disobeyfi/badge-2019/hardware/kicad/rev2badge.sch

## KiCad design hardware/kicad/rev2badge.sch (2019-03-05)

Schematic: rev2badge.sch

Parts:
BT1: Battery; AAAx2holder
C1, C2, C3, C4, C5, C6, C7, C8, C9: 10u; C_0603
D1, D3, D4, D5, D6, D7: LED_ARGB; ARGB-0606
D2: LED_Small_ALT; LED_1206_HandSoldering
J1: USB_OTG; MICROUSB
J2: Conn_01x30; ER-CON30HB-1
J3, J4, J5, J6, J7, J8: TEST_1P; Measurement_Point_Round-SMD-Pad_Big
J9: Conn_02x02_Counter_Clockwise; Pin_Header_Straight_2x02_Pitch2.54mm
J10: Conn_01x06; Pin_Header_Straight_1x06_Pitch2.54mm
J11: Conn_01x05; Pin_Header_Straight_1x05_Pitch2.54mm
L1: L; C_0805
LS1: Speaker_Crystal; Piezo-PS1240P02BT
R1, R2, R3, R14: 330R; R_0603
R4, R16: 2k; R_0603
R5: 1k; R_0603
R6, R7, R11, R12, R13, R15: 100k; R_0603
R8, R9, R10: 4.7k; R_0603
SW1, SW2: SW_Push; SW_SPST_FSMSM
U1: ESP32-WROOM
U2: SAMD21G15A-MU; QFN-48-1EP_7x7mm_Pitch0.5mm
U3: AZ1117-3.3; SOT-223-3_TabPin2
U4: TSMP58000; IRReceiver_Vishay_MINICAST-3pin
U5: AAT1217ICA-3.3-T1; TSOT-23-6
U6: MCP6001; SOT-23-5
