disobeyfi/badge-2019/src/samd/1.6.18/variants/disobey/variant.cpp

/*
  Copyright (c) 2014-2015 Arduino LLC.  All right reserved.

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
  You should have received a copy of the GNU Lesser General Public
  License along with this library; if not, write to the Free Software
  Foundation, Inc., 51 Franklin St, Fifth Floor, Boston, MA  02110-1301  USA
*/


#include "variant.h"

/*
 * Pins descriptions
 */
const PinDescription g_APinDescription[]=
{
  // 0..13 - Digital pins
  // ----------------------
  // 0/1 - SERCOM/UART (Serial1)
  { PORTA,  1, PIO_SERCOM_ALT, 0, No_ADC_Channel, NOT_ON_PWM, NOT_ON_TIMER, EXTERNAL_INT_NONE }, // PA01 / UART RX
  { PORTA,  0, PIO_SERCOM_ALT, 0, No_ADC_Channel, NOT_ON_PWM, NOT_ON_TIMER, EXTERNAL_INT_NONE }, // PA00 / UART TX

  // 2..24
  // Digital Low
  { PORTA,  18, PIO_TIMER_ALT, (PIN_ATTR_DIGITAL|PIN_ATTR_PWM|PIN_ATTR_TIMER_ALT), No_ADC_Channel, PWM0_CH2, TCC0_CH2, EXTERNAL_INT_NONE }, // D2 LED
  { PORTA,  23, PIO_TIMER_ALT, (PIN_ATTR_DIGITAL|PIN_ATTR_PWM|PIN_ATTR_TIMER_ALT), No_ADC_Channel, PWM0_CH5, TCC0_CH5, EXTERNAL_INT_NONE }, // D3 LED
  { PORTA,  22, PIO_TIMER_ALT, (PIN_ATTR_DIGITAL|PIN_ATTR_PWM|PIN_ATTR_TIMER_ALT), No_ADC_Channel, PWM0_CH4, TCC0_CH4, EXTERNAL_INT_NONE }, // D4 LED
  { PORTA,  21, PIO_TIMER_ALT, (PIN_ATTR_DIGITAL|PIN_ATTR_PWM|PIN_ATTR_TIMER_ALT), No_ADC_Channel, PWM0_CH7, TCC0_CH7, EXTERNAL_INT_NONE }, // D5 LED
  { PORTA,  20, PIO_DIGITAL, (PIN_ATTR_DIGITAL), No_ADC_Channel, NOT_ON_PWM, NOT_ON_TIMER, EXTERNAL_INT_NONE }, // D6 LED
  { PORTA,  19, PIO_TIMER_ALT, (PIN_ATTR_DIGITAL|PIN_ATTR_PWM|PIN_ATTR_TIMER_ALT), No_ADC_Channel, PWM0_CH3, TCC0_CH3, EXTERNAL_INT_NONE }, // D7 LED
  { PORTA,  17, PIO_TIMER, (PIN_ATTR_DIGITAL|PIN_ATTR_PWM|PIN_ATTR_TIMER), No_ADC_Channel, PWM2_CH1, TCC2_CH1, EXTERNAL_INT_NONE }, // D8 LED R
  { PORTA,  12, PIO_TIMER, (PIN_ATTR_DIGITAL|PIN_ATTR_PWM|PIN_ATTR_TIMER), No_ADC_Channel, PWM2_CH0, TCC2_CH0, EXTERNAL_INT_NONE }, // D9 LED G
  { PORTA,  16, PIO_TIMER_ALT, (PIN_ATTR_DIGITAL|PIN_ATTR_PWM|PIN_ATTR_TIMER_ALT), No_ADC_Channel, PWM0_CH6, TCC0_CH6, EXTERNAL_INT_NONE }, // D10 LED B
  { PORTA, 28, PIO_DIGITAL, (PIN_ATTR_DIGITAL), No_ADC_Channel, NOT_ON_PWM, NOT_ON_TIMER, EXTERNAL_INT_8 },                    // D11 ESPBL
  { PORTA, 27, PIO_DIGITAL, (PIN_ATTR_DIGITAL), No_ADC_Channel, NOT_ON_PWM, NOT_ON_TIMER, EXTERNAL_INT_15 },                    // D12 ESPRST
  { PORTA, 13, PIO_DIGITAL, (PIN_ATTR_DIGITAL), No_ADC_Channel, NOT_ON_PWM, NOT_ON_TIMER, EXTERNAL_INT_13 },                    // D13 IRLED
  { PORTB,  10, PIO_TIMER, (PIN_ATTR_DIGITAL|PIN_ATTR_PWM|PIN_ATTR_TIMER), No_ADC_Channel, PWM5_CH0, TC5_CH0, EXTERNAL_INT_NONE }, // D14 SPEAKER_OUT
  { PORTA, 10, PIO_DIGITAL, (PIN_ATTR_DIGITAL), No_ADC_Channel, NOT_ON_PWM, NOT_ON_TIMER, EXTERNAL_INT_10 },                    // D15 LCDRST
  { PORTA,  11, PIO_TIMER, (PIN_ATTR_DIGITAL|PIN_ATTR_PWM|PIN_ATTR_TIMER), No_ADC_Channel, PWM1_CH1, TCC1_CH1, EXTERNAL_INT_NONE }, // D16 LCDBL
  { PORTA,  14, PIO_DIGITAL, (PIN_ATTR_DIGITAL), No_ADC_Channel, NOT_ON_PWM, NOT_ON_TIMER, EXTERNAL_INT_13 }, // D17
  { PORTA,  8, PIO_SERCOM, PIN_ATTR_DIGITAL, No_ADC_Channel, NOT_ON_PWM, NOT_ON_TIMER, EXTERNAL_INT_NMI },                    // D18/SDA
  { PORTA,  9, PIO_SERCOM, PIN_ATTR_DIGITAL, No_ADC_Channel, NOT_ON_PWM, NOT_ON_TIMER, EXTERNAL_INT_9 },                    // D19/SCL
  { PORTB, 22, PIO_DIGITAL, (PIN_ATTR_DIGITAL), No_ADC_Channel, NOT_ON_PWM, NOT_ON_TIMER, EXTERNAL_INT_6 },                    // D20
  { PORTB, 23, PIO_DIGITAL, (PIN_ATTR_DIGITAL), No_ADC_Channel, NOT_ON_PWM, NOT_ON_TIMER, EXTERNAL_INT_7 },                    // D21  
  { PORTA, 10, PIO_DIGITAL, (PIN_ATTR_DIGITAL), No_ADC_Channel, NOT_ON_PWM, NOT_ON_TIMER, EXTERNAL_INT_10 },                    // D22 DO NOT USE
  { PORTA, 15, PIO_DIGITAL, (PIN_ATTR_DIGITAL), No_ADC_Channel, NOT_ON_PWM, NOT_ON_TIMER, EXTERNAL_INT_15 },                    // D23 (RN: This is the bootloader button SW2)
  { PORTB, 11, PIO_DIGITAL, (PIN_ATTR_DIGITAL), No_ADC_Channel, NOT_ON_PWM, NOT_ON_TIMER, EXTERNAL_INT_11 },                    // D24
  
   // 25..34 - Analog pins
  // --------------------
  { PORTB,  3, PIO_ANALOG, (PIN_ATTR_DIGITAL|PIN_ATTR_ANALOG), ADC_Channel11, NOT_ON_PWM, NOT_ON_TIMER, EXTERNAL_INT_3 },        // A1/D25
  { PORTA,  2, PIO_ANALOG, (PIN_ATTR_DIGITAL|PIN_ATTR_ANALOG), ADC_Channel0, NOT_ON_PWM, NOT_ON_TIMER, EXTERNAL_INT_2 },        // A4/D26
  { PORTA,  3, PIO_ANALOG, (PIN_ATTR_DIGITAL|PIN_ATTR_ANALOG), ADC_Channel1, NOT_ON_PWM, NOT_ON_TIMER, EXTERNAL_INT_3 },        // A5/D27
  { PORTA,  4, PIO_ANALOG, (PIN_ATTR_DIGITAL|PIN_ATTR_ANALOG), ADC_Channel4, NOT_ON_PWM, NOT_ON_TIMER, EXTERNAL_INT_4 },        // A6/D28
  { PORTA,  5, PIO_ANALOG, (PIN_ATTR_DIGITAL|PIN_ATTR_ANALOG), ADC_Channel5, NOT_ON_PWM, NOT_ON_TIMER, EXTERNAL_INT_5 },        // A7/D29
  { PORTA,  6, PIO_ANALOG, (PIN_ATTR_DIGITAL|PIN_ATTR_ANALOG), ADC_Channel6, NOT_ON_PWM, NOT_ON_TIMER, EXTERNAL_INT_6 },        // A8/D30
  { PORTA,  7, PIO_ANALOG, (PIN_ATTR_DIGITAL|PIN_ATTR_ANALOG), ADC_Channel7, NOT_ON_PWM, NOT_ON_TIMER, EXTERNAL_INT_7 },        // A9/D31
  { PORTB,  9, PIO_ANALOG, (PIN_ATTR_DIGITAL|PIN_ATTR_ANALOG), ADC_Channel3, NOT_ON_PWM, NOT_ON_TIMER, EXTERNAL_INT_8 },        // A3/D32
  { PORTB,  8, PIO_ANALOG, (PIN_ATTR_DIGITAL|PIN_ATTR_ANALOG), ADC_Channel2, NOT_ON_PWM, NOT_ON_TIMER, EXTERNAL_INT_9 },        // A2/D33
  { PORTB,  2, PIO_ANALOG, (PIN_ATTR_DIGITAL|PIN_ATTR_ANALOG), ADC_Channel10, NOT_ON_PWM, NOT_ON_TIMER, EXTERNAL_INT_2 },        // A0/D34
  
  //35/36 - SWD
  { PORTA, 30, PIO_COM, PIN_ATTR_NONE, No_ADC_Channel, NOT_ON_PWM, NOT_ON_TIMER, EXTERNAL_INT_NONE }, // D35 SWCLK
  { PORTA, 31, PIO_COM, PIN_ATTR_NONE, No_ADC_Channel, NOT_ON_PWM, NOT_ON_TIMER, EXTERNAL_INT_NONE }, // D35 SWDIO

  
  // 37..38 - USB
  // --------------------  
  { PORTA, 24, PIO_COM, PIN_ATTR_NONE, No_ADC_Channel, NOT_ON_PWM, NOT_ON_TIMER, EXTERNAL_INT_NONE }, // USB/DM
  { PORTA, 25, PIO_COM, PIN_ATTR_NONE, No_ADC_Channel, NOT_ON_PWM, NOT_ON_TIMER, EXTERNAL_INT_NONE }, // USB/DP

} ;

const void* g_apTCInstances[TCC_INST_NUM+TC_INST_NUM]={ TCC0, TCC1, TCC2, TC5} ;

// Multi-serial objects instantiation
SERCOM sercom0( SERCOM0 ) ;
SERCOM sercom1( SERCOM1 ) ;
SERCOM sercom2( SERCOM2 ) ;
SERCOM sercom3( SERCOM3 ) ;
SERCOM sercom4( SERCOM4 ) ;
SERCOM sercom5( SERCOM5 ) ;

Uart Serial1( &sercom1, PIN_SERIAL1_RX, PIN_SERIAL1_TX, PAD_SERIAL1_RX, PAD_SERIAL1_TX ) ;

void SERCOM1_Handler()
{
  Serial1.IrqHandler();
}
