disobeyfi/badge-2019/src/samd/bootloader/example-apps/vcp/main.c

/*
 * Copyright (c) 2017, Alex Taradov <alex@taradov.com>
 * All rights reserved.
 *
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
 * THIS SOFTWARE IS PROVIDED BY THE COPYRIGHT HOLDERS AND CONTRIBUTORS "AS IS"
 * AND ANY EXPRESS OR IMPLIED WARRANTIES, INCLUDING, BUT NOT LIMITED TO, THE
 * IMPLIED WARRANTIES OF MERCHANTABILITY AND FITNESS FOR A PARTICULAR PURPOSE
 * ARE DISCLAIMED. IN NO EVENT SHALL THE COPYRIGHT HOLDER OR CONTRIBUTORS BE
 * LIABLE FOR ANY DIRECT, INDIRECT, INCIDENTAL, SPECIAL, EXEMPLARY, OR
 * CONSEQUENTIAL DAMAGES (INCLUDING, BUT NOT LIMITED TO, PROCUREMENT OF
 * SUBSTITUTE GOODS OR SERVICES; LOSS OF USE, DATA, OR PROFITS; OR BUSINESS
 * INTERRUPTION) HOWEVER CAUSED AND ON ANY THEORY OF LIABILITY, WHETHER IN
 * CONTRACT, STRICT LIABILITY, OR TORT (INCLUDING NEGLIGENCE OR OTHERWISE)
 * ARISING IN ANY WAY OUT OF THE USE OF THIS SOFTWARE, EVEN IF ADVISED OF THE
 * POSSIBILITY OF SUCH DAMAGE.
 */

/*- Includes ----------------------------------------------------------------*/
#include <stdlib.h>
#include <stdint.h>
#include <stdbool.h>
#include <stdalign.h>
#include <string.h>
#include "samd11.h"
#include "hal_gpio.h"
#include "nvm_data.h"
#include "usb.h"
#include "uart.h"
#define GPIO_ON(pin) (PORT->Group[0].OUTSET.reg = (1<<(pin)))
#define GPIO_OFF(pin) (PORT->Group[0].OUTCLR.reg = (1<<(pin)))


/*- Definitions -------------------------------------------------------------*/
#define USB_BUFFER_SIZE        64
#define UART_WAIT_TIMEOUT      10 // ms

// NOTE: Set both rising and falling edge times to 0 to disable edge detection.
HAL_GPIO_PIN(STATUS,           A, 9);
#define STATUS_INACTIVE_STATE  0 // 0 - Low, 1 - High, 2 - Hi-Z
#define STATUS_ACTIVE_STATE    1 // 0 - Low, 1 - High, 2 - Hi-Z
#define STATUS_RISING_EDGE     0 // ms
#define STATUS_FALLING_EDGE    0 // ms

/*- Variables ---------------------------------------------------------------*/
static alignas(4) uint8_t app_recv_buffer[USB_BUFFER_SIZE];
static alignas(4) uint8_t app_send_buffer[USB_BUFFER_SIZE];
static int app_recv_buffer_size = 0;
static int app_recv_buffer_ptr = 0;
static int app_send_buffer_ptr = 0;
static bool app_send_buffer_free = true;
static bool app_send_zlp = false;
static int app_system_time = 0;
static int app_uart_timeout = 0;
static bool app_status = false;
static int app_status_timeout = 0;

/*- Implementations ---------------------------------------------------------*/

//-----------------------------------------------------------------------------
static void sys_init(void)
{
  uint32_t coarse, fine;
  uint32_t sn = 0;

  NVMCTRL->CTRLB.reg = NVMCTRL_CTRLB_CACHEDIS | NVMCTRL_CTRLB_RWS(2);

  SYSCTRL->INTFLAG.reg = SYSCTRL_INTFLAG_BOD33RDY | SYSCTRL_INTFLAG_BOD33DET |
      SYSCTRL_INTFLAG_DFLLRDY;

  coarse = NVM_READ_CAL(NVM_DFLL48M_COARSE_CAL);
  fine = NVM_READ_CAL(NVM_DFLL48M_FINE_CAL);

  SYSCTRL->DFLLCTRL.reg = 0; // See Errata 9905
  while (0 == (SYSCTRL->PCLKSR.reg & SYSCTRL_PCLKSR_DFLLRDY));

  SYSCTRL->DFLLMUL.reg = SYSCTRL_DFLLMUL_MUL(48000);
  SYSCTRL->DFLLVAL.reg = SYSCTRL_DFLLVAL_COARSE(coarse) | SYSCTRL_DFLLVAL_FINE(fine);

  SYSCTRL->DFLLCTRL.reg = SYSCTRL_DFLLCTRL_ENABLE | SYSCTRL_DFLLCTRL_USBCRM |
      SYSCTRL_DFLLCTRL_MODE | SYSCTRL_DFLLCTRL_CCDIS;

  while (0 == (SYSCTRL->PCLKSR.reg & SYSCTRL_PCLKSR_DFLLRDY));

  GCLK->GENCTRL.reg = GCLK_GENCTRL_ID(0) | GCLK_GENCTRL_SRC(GCLK_SOURCE_DFLL48M) |
      GCLK_GENCTRL_RUNSTDBY | GCLK_GENCTRL_GENEN;
  while (GCLK->STATUS.reg & GCLK_STATUS_SYNCBUSY);

  sn ^= *(volatile uint32_t *)0x0080a00c;
  sn ^= *(volatile uint32_t *)0x0080a040;
  sn ^= *(volatile uint32_t *)0x0080a044;
  sn ^= *(volatile uint32_t *)0x0080a048;

  for (int i = 0; i < 8; i++)
    usb_serial_number[i] = "0123456789ABCDEF"[(sn >> (i * 4)) & 0xf];

  usb_serial_number[9] = 0;
}

//-----------------------------------------------------------------------------
static void sys_time_init(void)
{
  SysTick->VAL = 0;
  SysTick->LOAD = F_CPU / 1000ul;
  SysTick->CTRL = SysTick_CTRL_ENABLE_Msk;
  app_system_time = 0;
}

//-----------------------------------------------------------------------------
static void sys_time_task(void)
{
  if (SysTick->CTRL & SysTick_CTRL_COUNTFLAG_Msk)
    app_system_time++;
}

//-----------------------------------------------------------------------------
static int get_system_time(void)
{
  return app_system_time;
}

//-----------------------------------------------------------------------------
static void set_status_state(bool active)
{
  if (active)
  {
  #if STATUS_ACTIVE_STATE == 0
    HAL_GPIO_STATUS_out();
    HAL_GPIO_STATUS_clr();
  #elif STATUS_ACTIVE_STATE == 1
    HAL_GPIO_STATUS_out();
    HAL_GPIO_STATUS_set();
  #else
    HAL_GPIO_STATUS_in();
  #endif
  }
  else
  {
  #if STATUS_INACTIVE_STATE == 0
    HAL_GPIO_STATUS_out();
    HAL_GPIO_STATUS_clr();
  #elif STATUS_INACTIVE_STATE == 1
    HAL_GPIO_STATUS_out();
    HAL_GPIO_STATUS_set();
  #else
    HAL_GPIO_STATUS_in();
  #endif
  }
}

//-----------------------------------------------------------------------------
static void update_status(bool status)
{
#if STATUS_RISING_EDGE > 0
  if (false == app_status && true == status)
  {
    set_status_state(true);
    app_status_timeout = get_system_time() + STATUS_RISING_EDGE;
  }
#endif

#if STATUS_FALLING_EDGE > 0
  if (true == app_status && false == status)
  {
    set_status_state(true);
    app_status_timeout = get_system_time() + STATUS_FALLING_EDGE;
  }
#endif

#if STATUS_RISING_EDGE == 0 && STATUS_FALLING_EDGE == 0
  set_status_state(status);
#endif

  app_status = status;
}

//-----------------------------------------------------------------------------
static void status_task(void)
{
  if (app_status_timeout && get_system_time() > app_status_timeout)
  {
    set_status_state(false);
    app_status_timeout = 0;
  }
}

//-----------------------------------------------------------------------------
void usb_cdc_send_callback(void)
{
  app_send_buffer_free = true;
}

//-----------------------------------------------------------------------------
static void send_buffer(void)
{
  app_send_buffer_free = false;
  app_send_zlp = (USB_BUFFER_SIZE == app_send_buffer_ptr);

  usb_cdc_send(app_send_buffer, app_send_buffer_ptr);

  app_send_buffer_ptr = 0;
}

//-----------------------------------------------------------------------------
void usb_cdc_recv_callback(int size)
{
  app_recv_buffer_ptr = 0;
  app_recv_buffer_size = size;
}

//-----------------------------------------------------------------------------
void usb_configuration_callback(int config)
{
  usb_cdc_recv(app_recv_buffer, sizeof(app_recv_buffer));
  (void)config;
}

//-----------------------------------------------------------------------------
void usb_cdc_line_coding_updated(usb_cdc_line_coding_t *line_coding)
{
if(line_coding->dwDTERate==1200){
  GPIO_ON(22);
}else{
  GPIO_OFF(22);
}
  uart_init(line_coding);
}

//-----------------------------------------------------------------------------
void usb_cdc_control_line_state_update(int line_state)
{
  update_status(line_state & USB_CDC_CTRL_SIGNAL_DTE_PRESENT);
}

//-----------------------------------------------------------------------------
static void tx_task(void)
{
  while (app_recv_buffer_size)
  {
    if (!uart_write_byte(app_recv_buffer[app_recv_buffer_ptr]))
      break;

    app_recv_buffer_ptr++;
    app_recv_buffer_size--;

    if (0 == app_recv_buffer_size)
      usb_cdc_recv(app_recv_buffer, sizeof(app_recv_buffer));
  }
}

//-----------------------------------------------------------------------------
static void rx_task(void)
{
  int byte;

  if (!app_send_buffer_free)
    return;

  while (uart_read_byte(&byte))
  {
    app_uart_timeout = get_system_time() + UART_WAIT_TIMEOUT;
    app_send_buffer[app_send_buffer_ptr++] = byte;

    if (USB_BUFFER_SIZE == app_send_buffer_ptr)
    {
      send_buffer();
      break;
    }
  }
}

//-----------------------------------------------------------------------------
static void uart_timer_task(void)
{
  if (app_uart_timeout && get_system_time() > app_uart_timeout)
  {
    if (app_send_zlp || app_send_buffer_ptr)
      send_buffer();

    app_uart_timeout = 0;
  }
}

//-----------------------------------------------------------------------------
void uart_serial_state_update(int state)
{
  usb_cdc_set_state(state);
}

//-----------------------------------------------------------------------------
int main(void)
{

 PORT->Group[0].DIRSET.reg = (1<<12)|(1<<13)|(1<<16)|(1<<17)|(1<<18)|
    (1<<19)|(1<<20)|(1<<21)|(1<<22)|(1<<23)|(1<<27)|(1<<28);
    
    GPIO_OFF(27);
    GPIO_OFF(28);
    
    
    GPIO_ON(12);
    GPIO_ON(16);
    GPIO_OFF(17);
    
    GPIO_OFF(18);
    GPIO_OFF(19);
    GPIO_OFF(20);
    GPIO_OFF(21);
    GPIO_OFF(22);
    GPIO_ON(23);
  sys_init();
  sys_time_init();
  usb_init();
  usb_cdc_init();
  set_status_state(false);

  while (1)
  {
    sys_time_task();
    usb_task();
    tx_task();
    rx_task();
    uart_timer_task();
    status_task();
  }

  return 0;
}
